olivierbrcknr/littleBigPrinter/LittleBigPrinter-Software/icons.h

static const uint8_t PROGMEM
  heart_icn[] =
    { B01100110,
      B10011001,
      B10000001,
      B10000001,
      B01000010,
      B00100100,
      B00011000,
      B00000000 },
  check_icn[] = 
    { B00000000,
      B00000001,
      B00000010,
      B00000100,
      B10001000,
      B01010000,
      B00100000,
      B00000000 },
  sinus_icn[] = 
    { B00000000,
      B00000000,
      B01100000,
      B10010000,
      B00001001,
      B00000110,
      B00000000,
      B00000000 },
  x_icn[] = 
    { B10000010,
      B01000100,
      B00101000,
      B00010000,
      B00101000,
      B01000100,
      B10000010,
      B00000000 },
  boot_icon[] = 
    { B00000001,
      B00000001,
      B00000001,
      B00000001,
      B00000001,
      B00000001,
      B00000001,
      B00000001 };
